dc1rdb/RockFinder/docs/IMG_20231223_130943.jpg

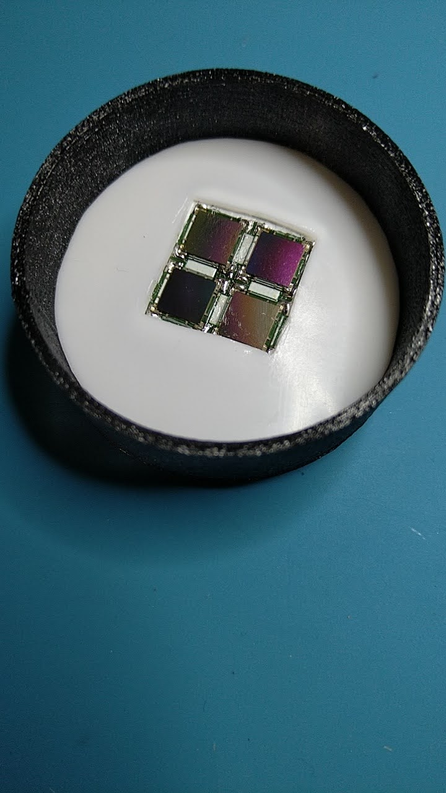
docs/IMG_20231223_130943.jpg
