dc1rdb/RockFinder/docs/V2_scintillator_assy.jpg

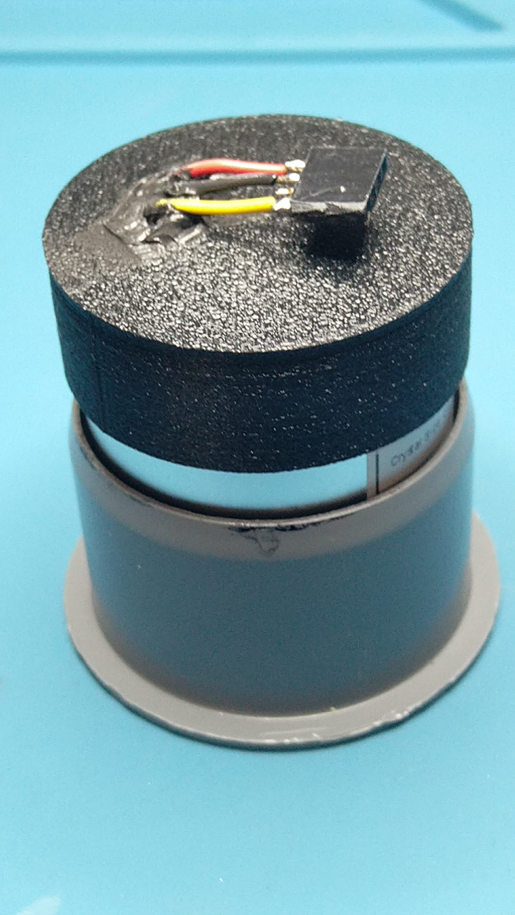
docs/V2_scintillator_assy.jpg
